denjhang/2xOPN-MegaMod-2023/2xOPN MegaMod v0.4/sshot-20231101-213623.png

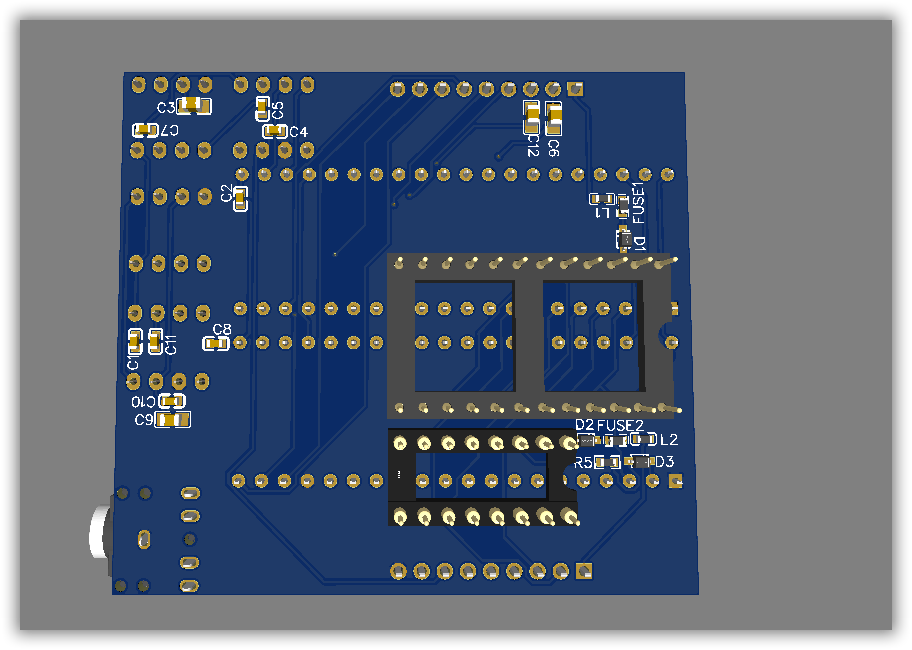
2xOPN MegaMod v0.4/sshot-20231101-213623.png
