denjhang/2xOPN-MegaMod-2023/2xOPN Mixer v0.2/sshot-20231115-143608.png

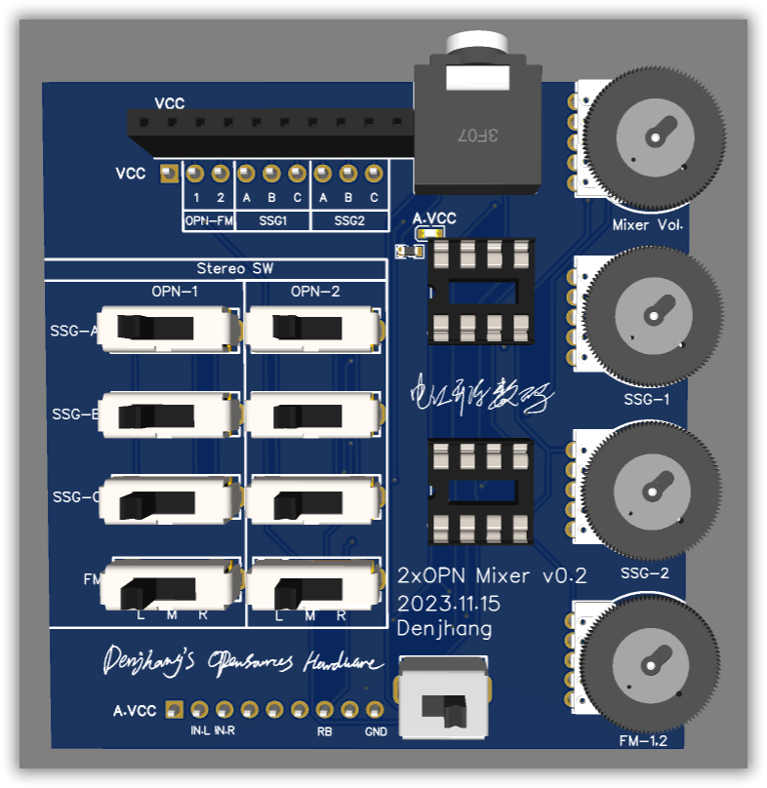
2xOPN Mixer v0.2/sshot-20231115-143608.png
