denjhang/2xOPN-MegaMod-2023/acb-gold-slice.png

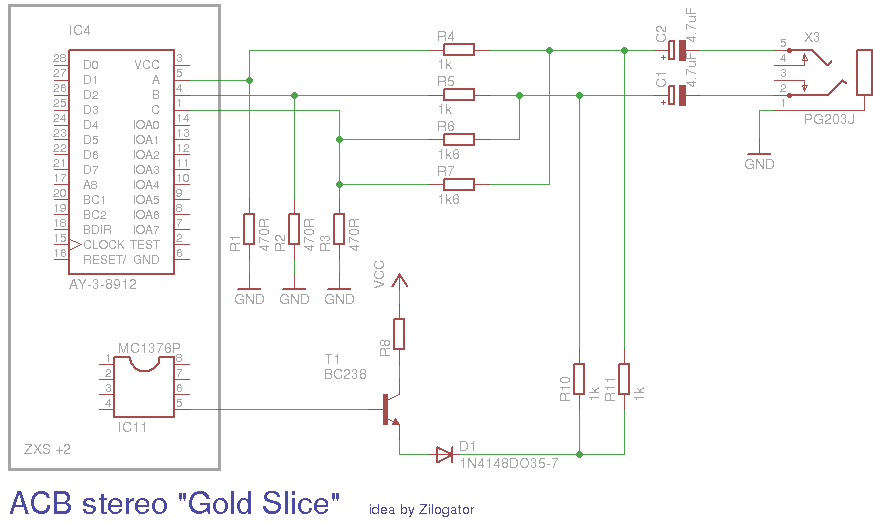
acb-gold-slice.png
