denjhang/2xOPN-MegaMod-2023/OPL2LPT-Replica-master/images/4.jpg

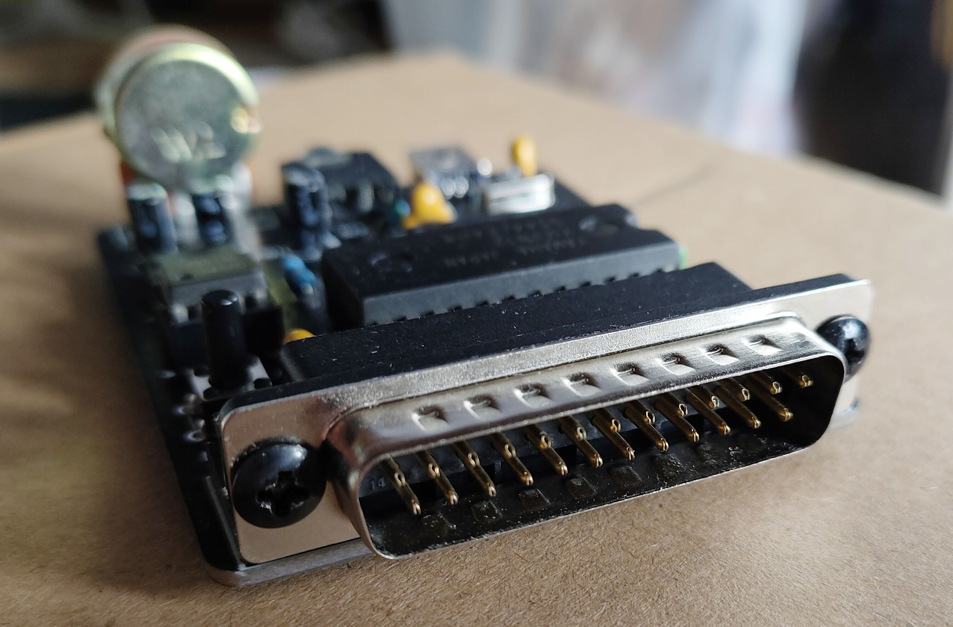
OPL2LPT-Replica-master/images/4.jpg
