denjhang/2xOPN-MegaMod-2023/rc2014-ym2149-main/R6-board-pic.jpg

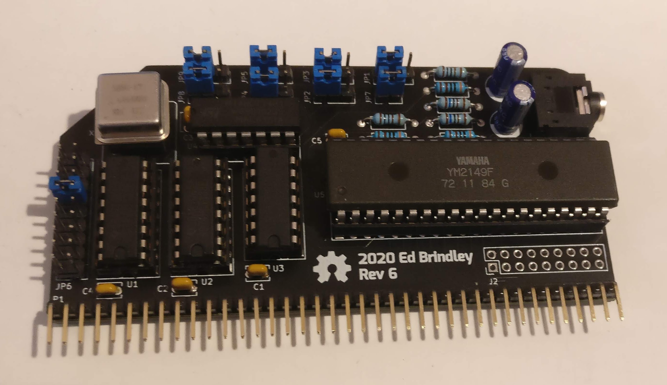
rc2014-ym2149-main/R6-board-pic.jpg
