denjhang/2xOPN-MegaMod-2023/rc2014-ym2149-main/r61-board-render.png

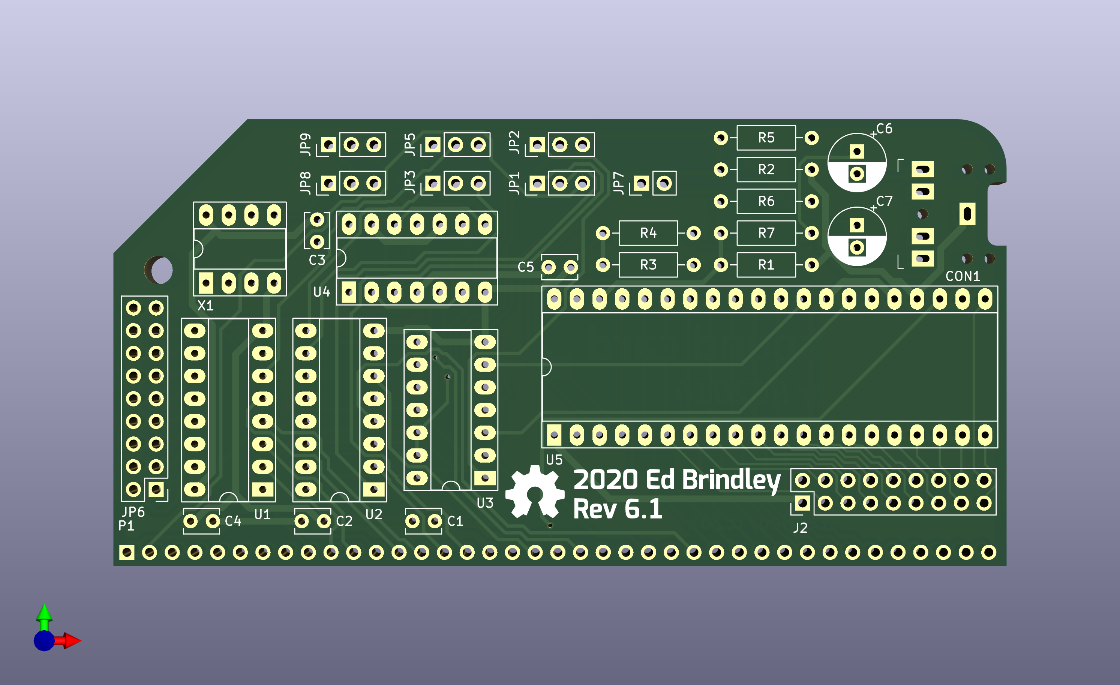
rc2014-ym2149-main/r61-board-render.png
