denjhang/2xOPN-MegaMod-2023/参考资料/ym2610-pcb-master/ym2610-pcb-master/photo/pcb2.jpg

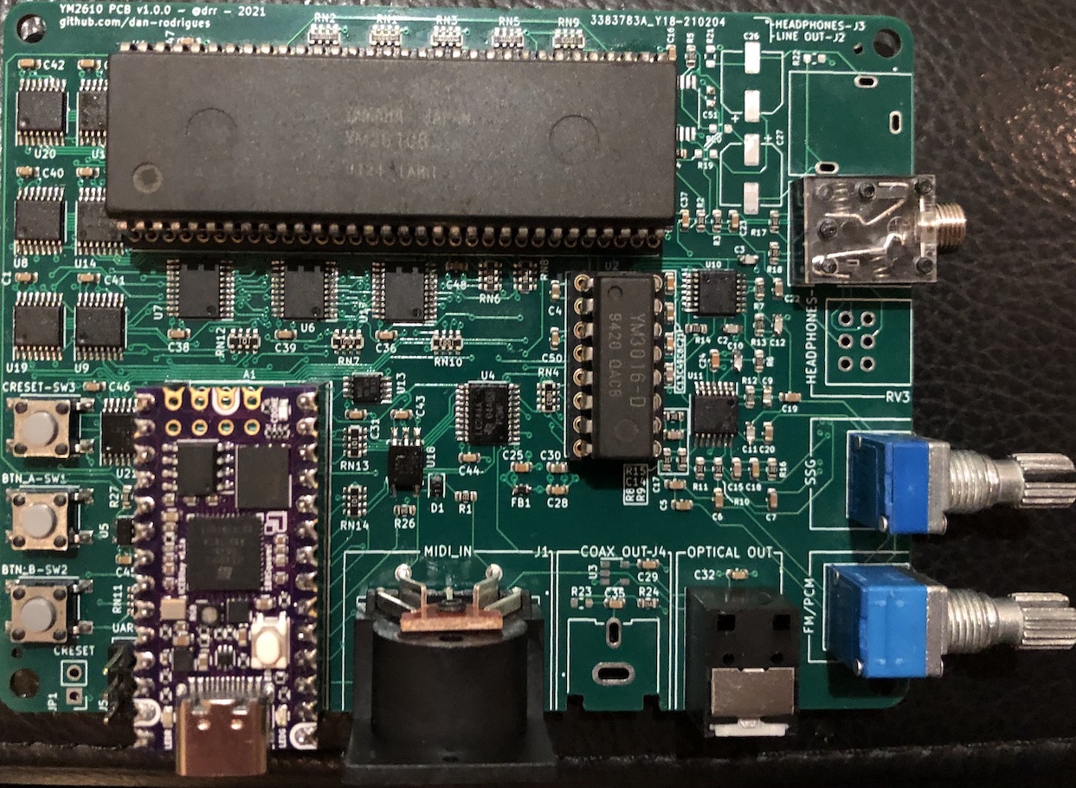
参考资料/ym2610-pcb-master/ym2610-pcb-master/photo/pcb2.jpg
