denjhang/2xOPN-MegaMod-2023/参考资料/ym2610-pcb-master/ym2610-pcb-master/pcb/ym2610-pcb.pdf

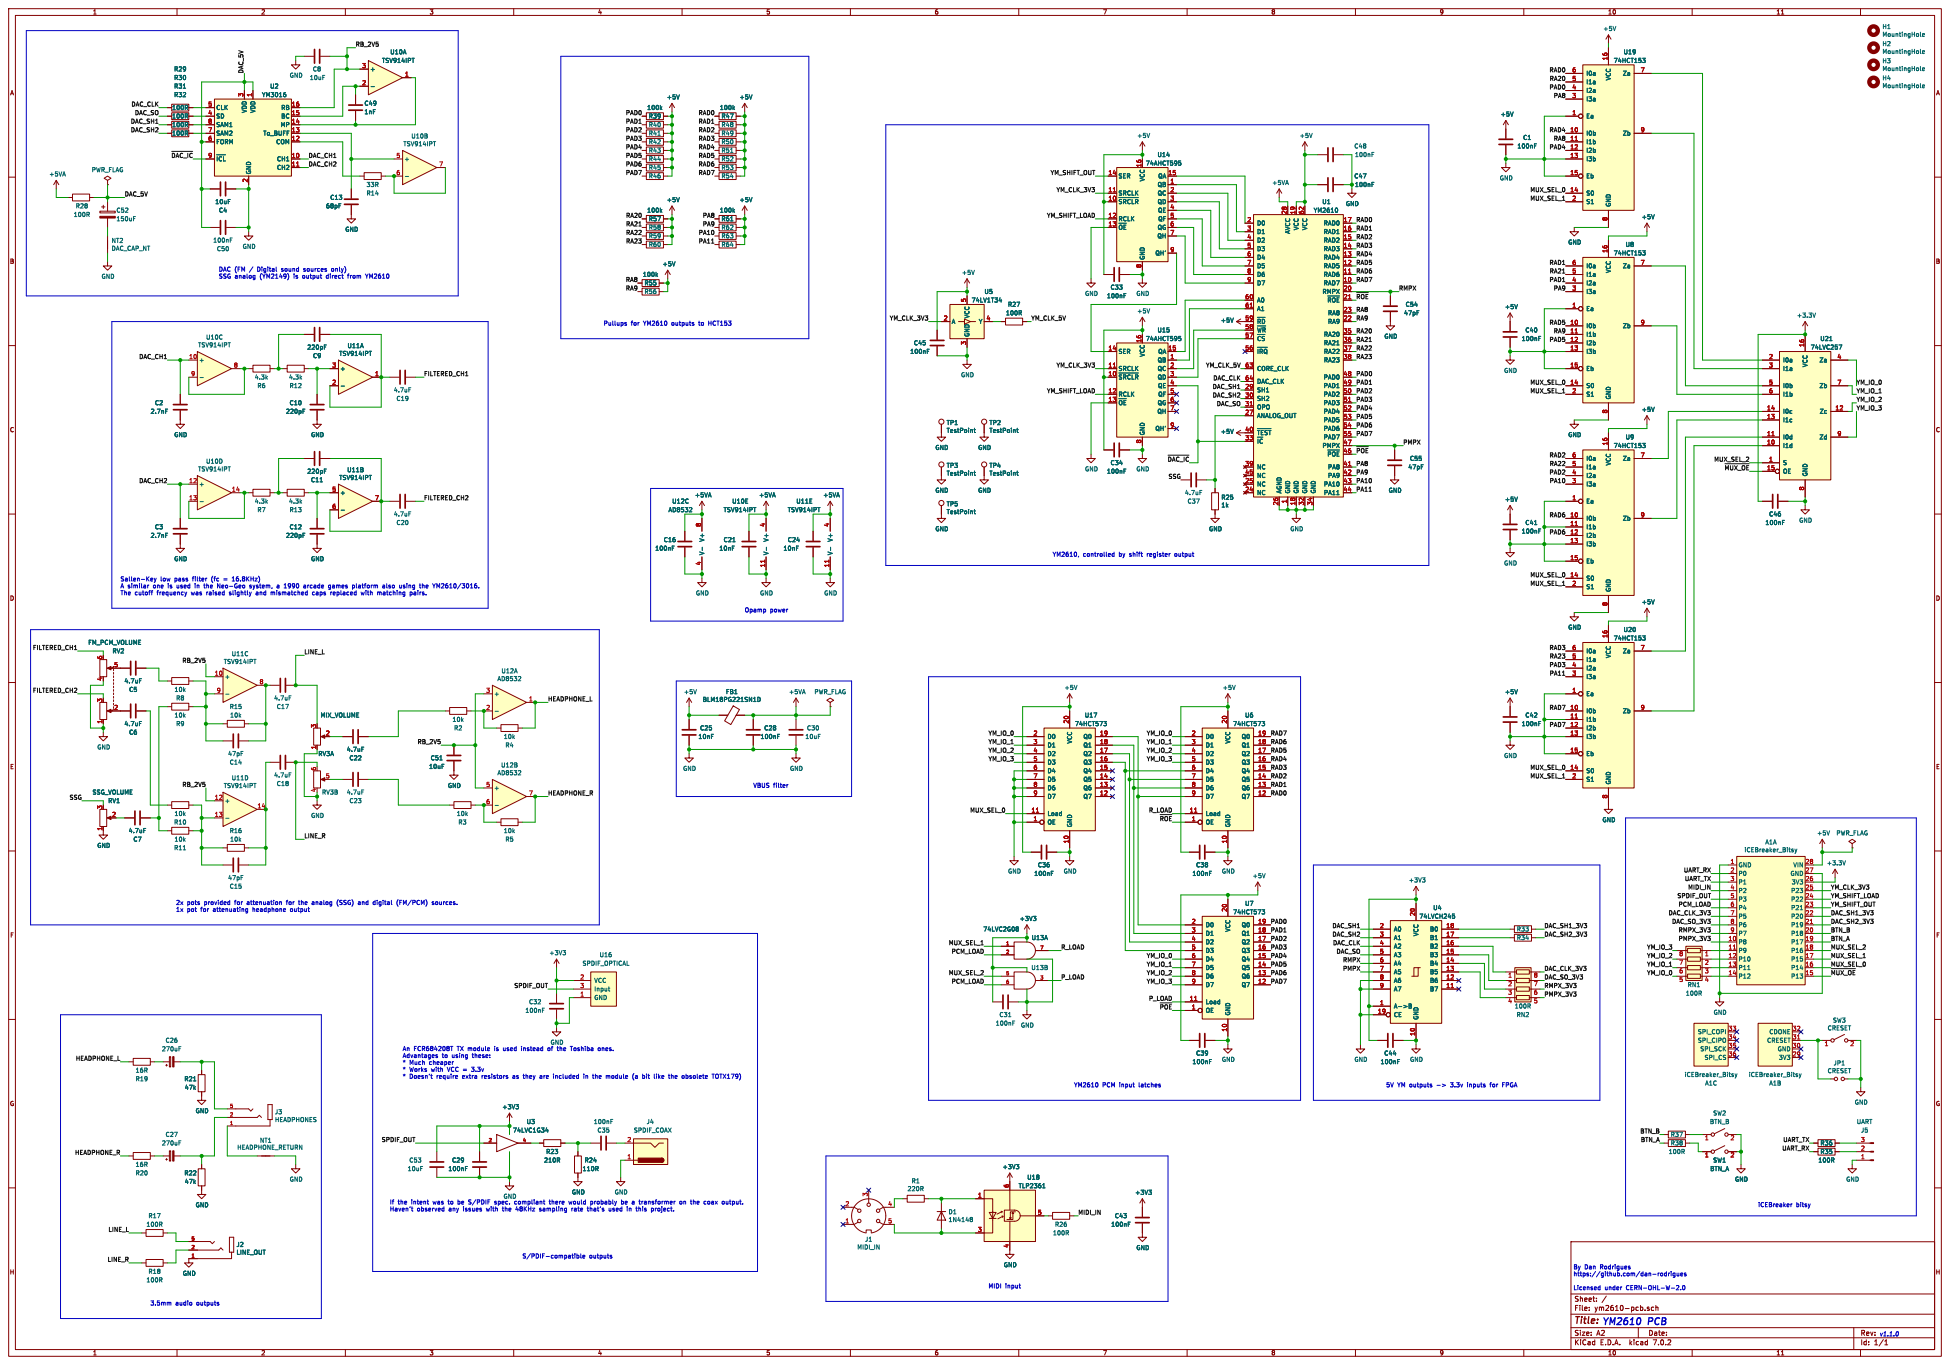
[picture p31: page 1]

H2 MountingHole H3 MountingHole H1 MountingHole H4 MountingHole

3 SD 4 CLK 5 FORM 6 SAM2 7 SAM1 8 ~{ICL} 9 U2 YM3016 GND GND

3 SD 4 CLK 5 FORM 6 SAM2 7 SAM1 8 ~{ICL} 9 GND

1 CH1 10 CH2 11 COM 12 To_BUFF 13 MP 14 BC 15 RB 16 GND
+5VA VDD

DAC (FM / Digital sound sources only) SSG analog (YM2149) is output direct from YM2610

Pullups for YM2610 outputs to HCT153

An FCR684208T TX module is used instead of the Toshiba ones. Advantages to using these: * Much cheaper * Works with VCC = 3.3v

https://github.com/dan-rodrigues Licensed under CERN-OHL-W-2.0

Id: 1/1 Title: File: ym2610-pcb.sch Sheet: /
YM2610 PCB
