denjhang/2xOPN-MegaMod-2023/2xOPN MegaMod v0.1/Schematic_Dual OPN MegaMod_2022-12-18.pdf

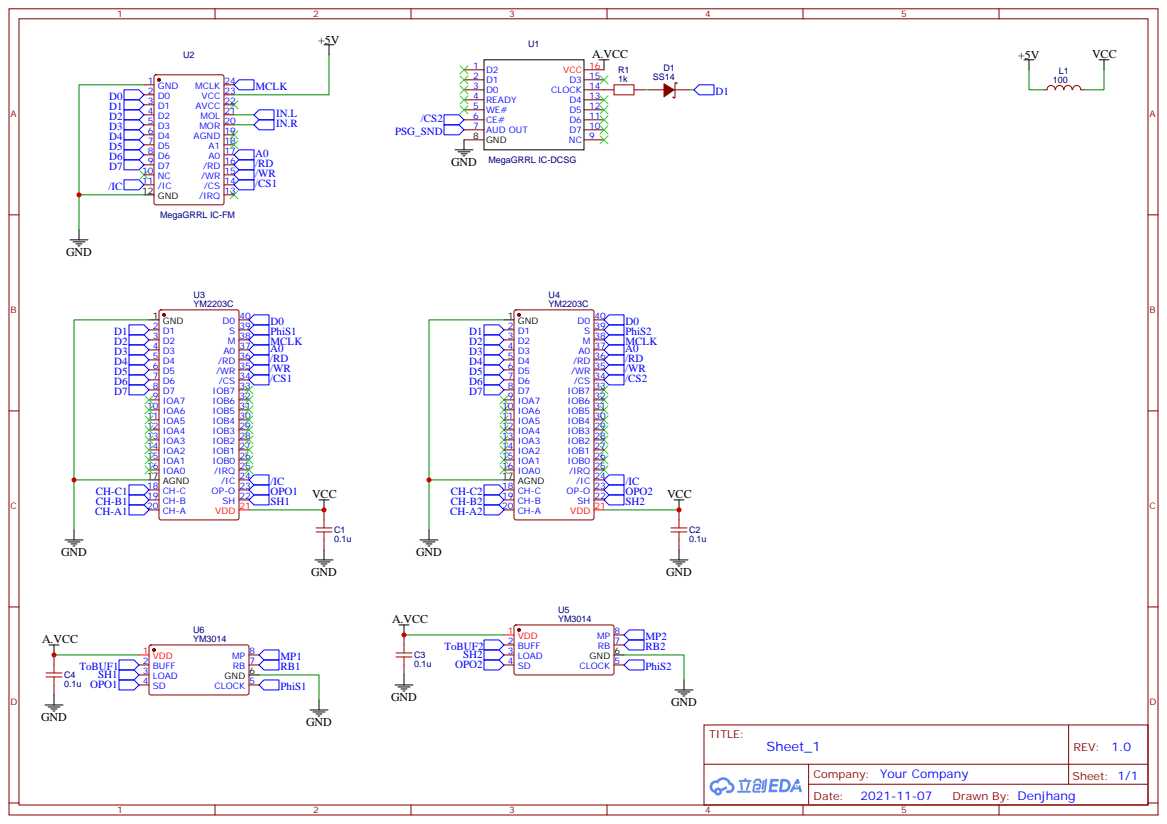
[picture p43: page 1]

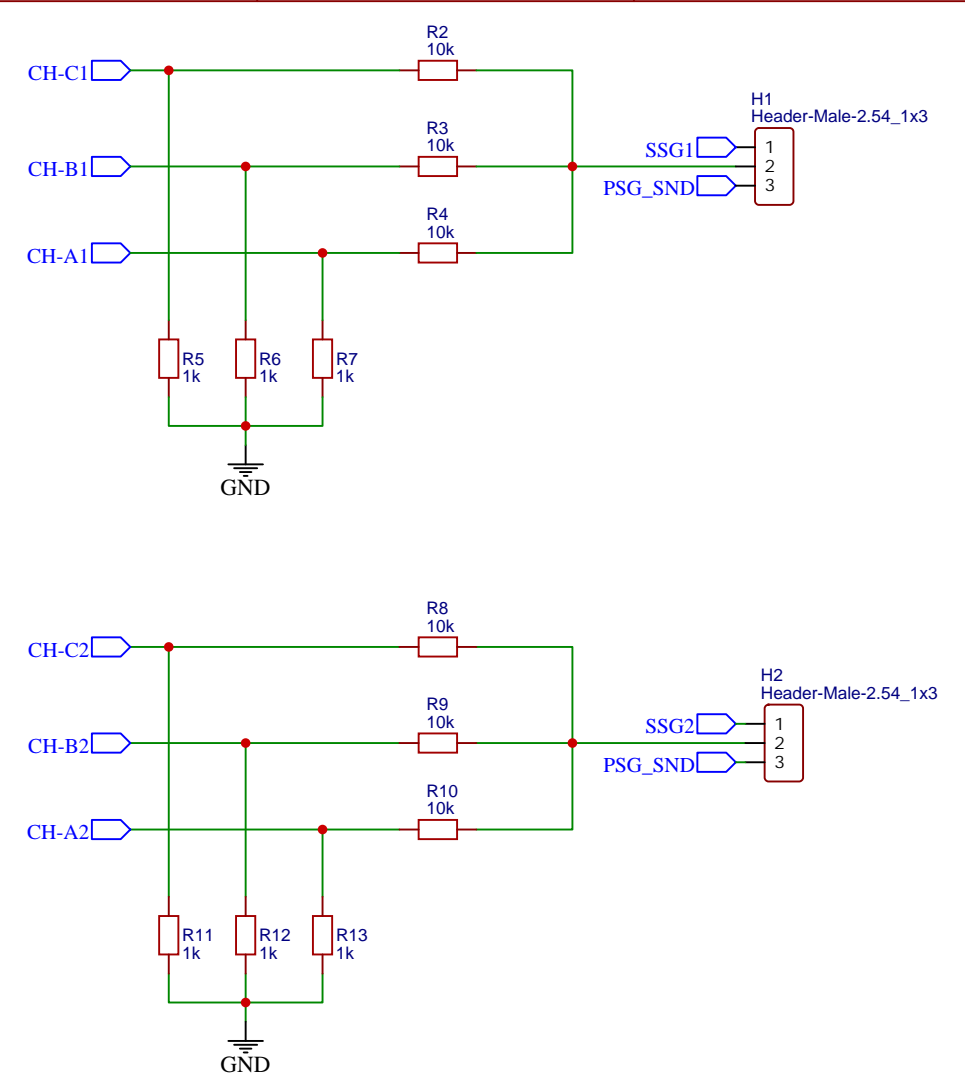
[picture p44: page 2]

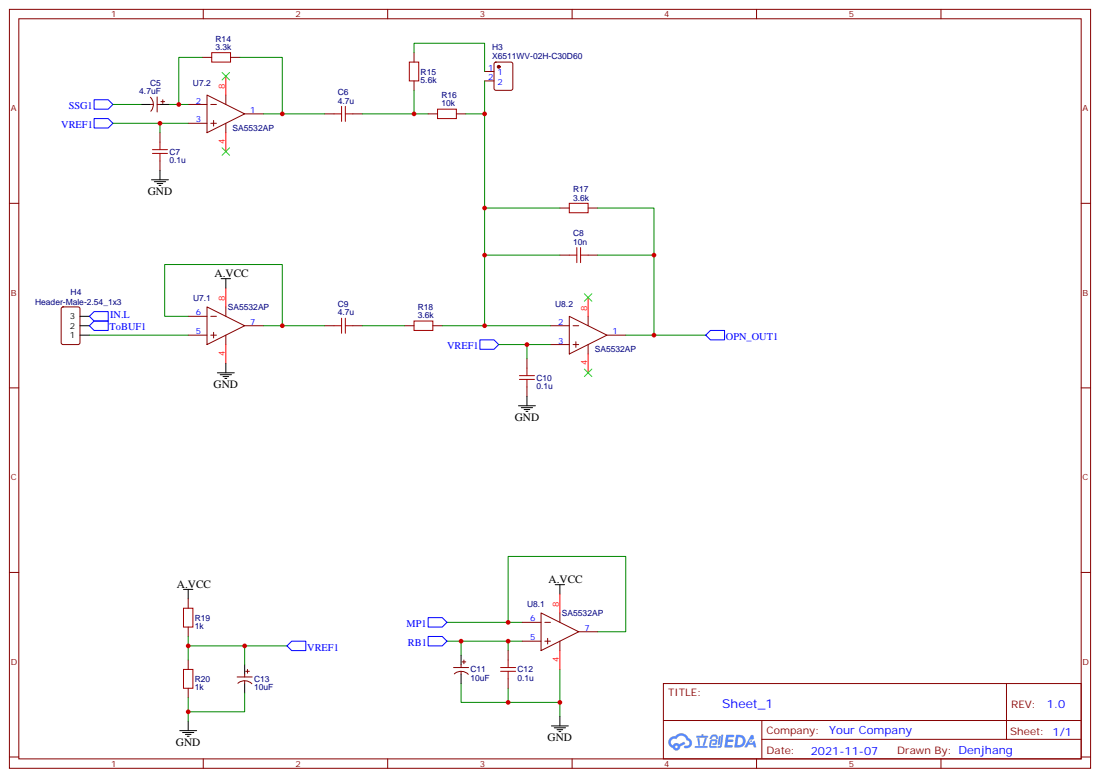
[picture p45: page 3]

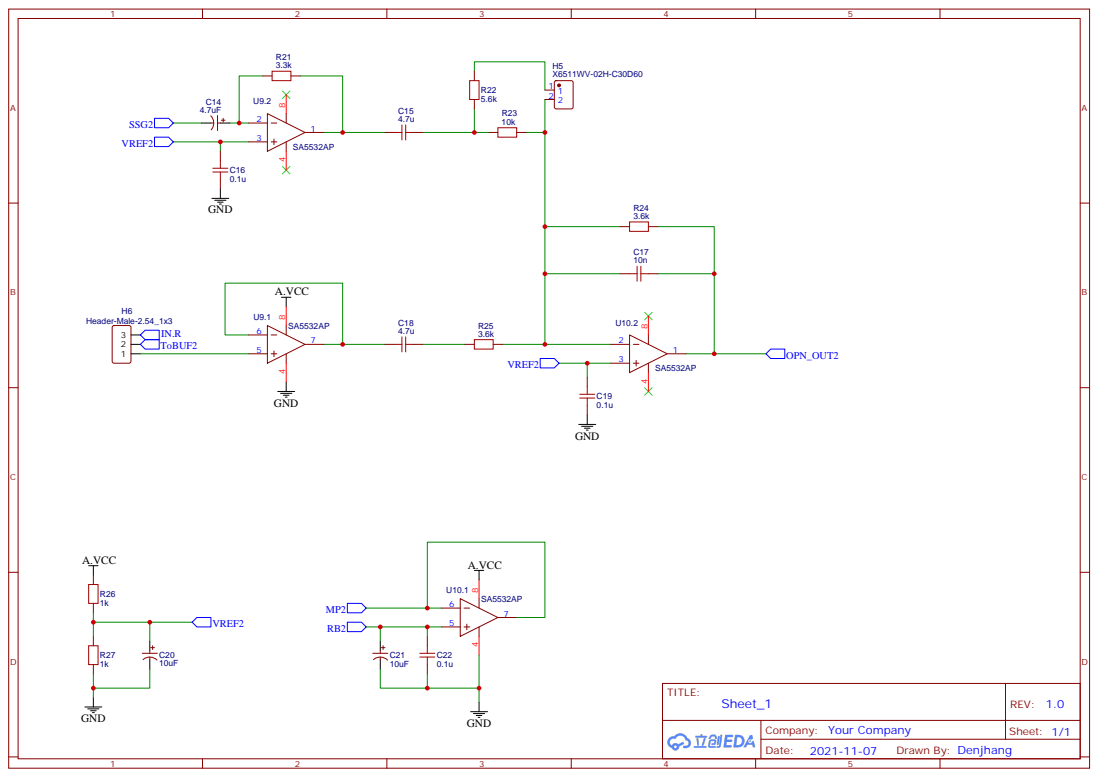
[picture p46: page 4]

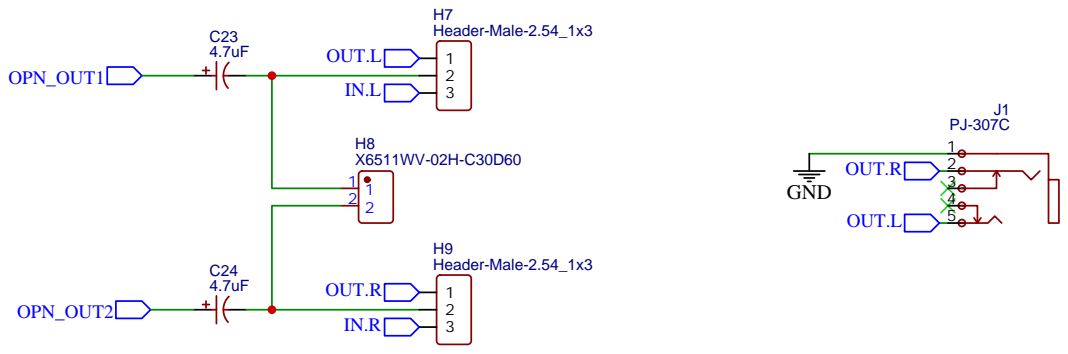
[picture p47: page 5]
