denjhang/2xOPN-MegaMod-2023/2xOPN MegaMod v0.2/Schematic_Dual OPN MegaMod v0.2_2023-01-27.pdf

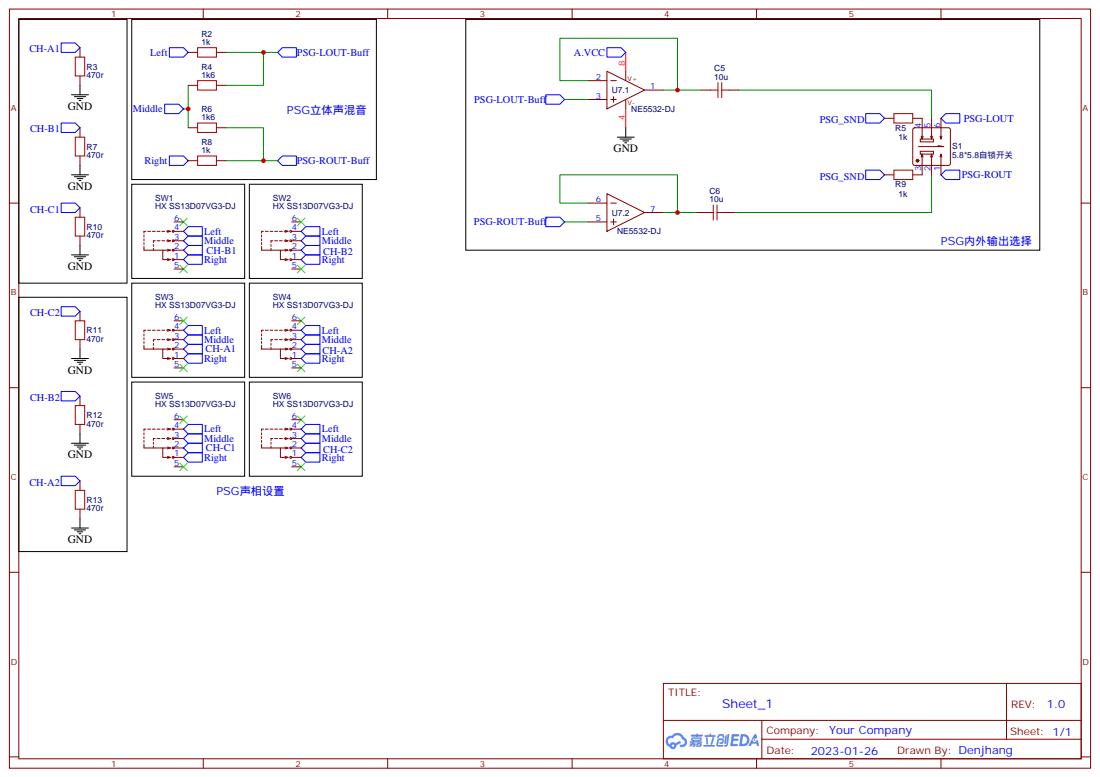
[picture p48: page 2]

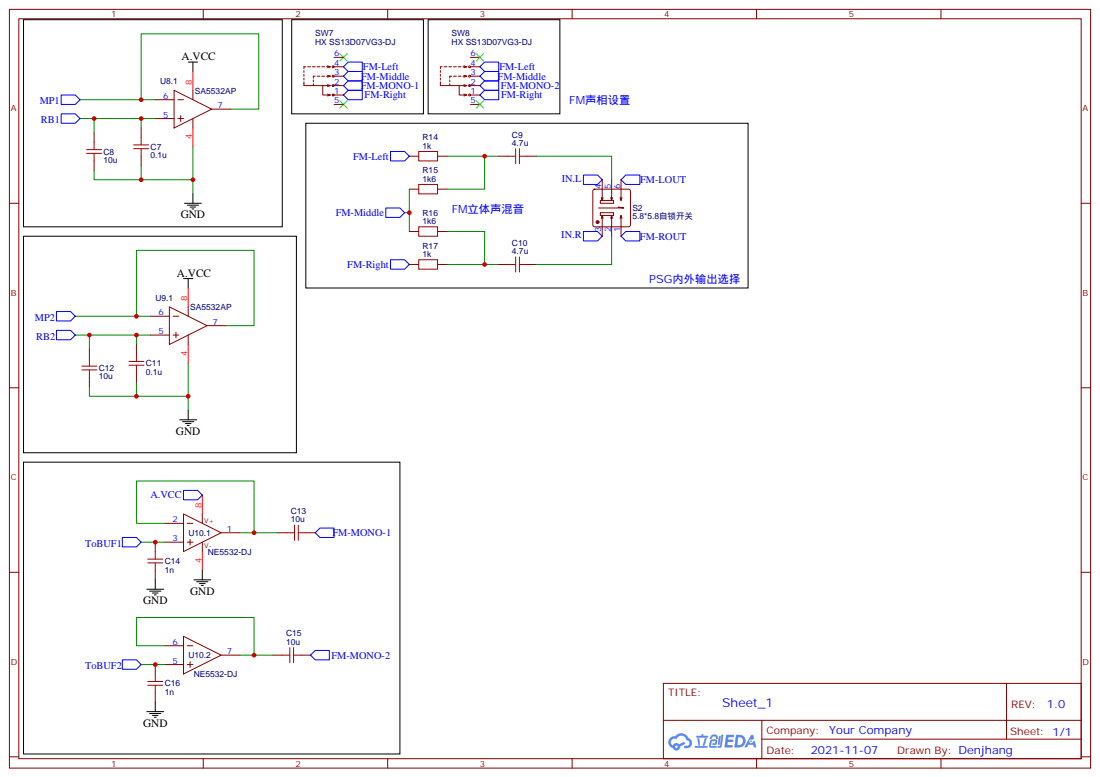
[picture p49: page 3]

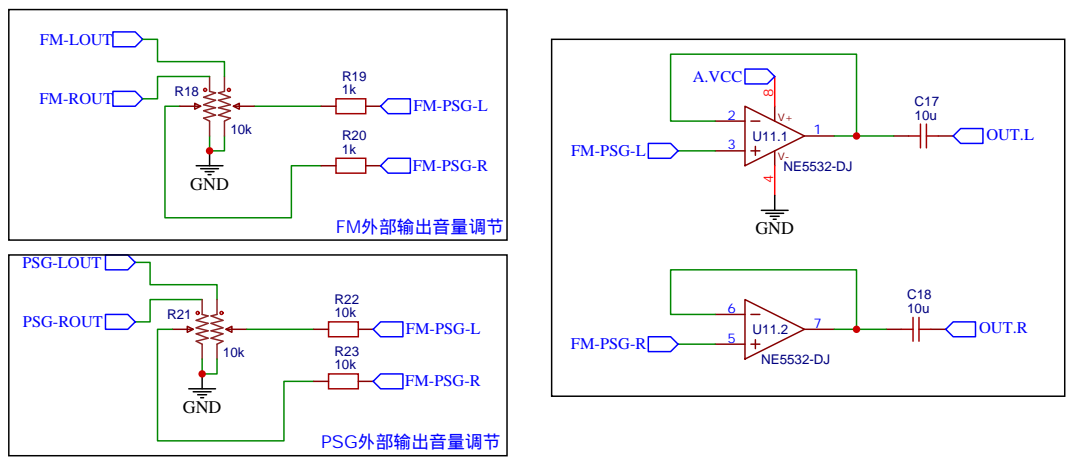
[picture p50: page 4]

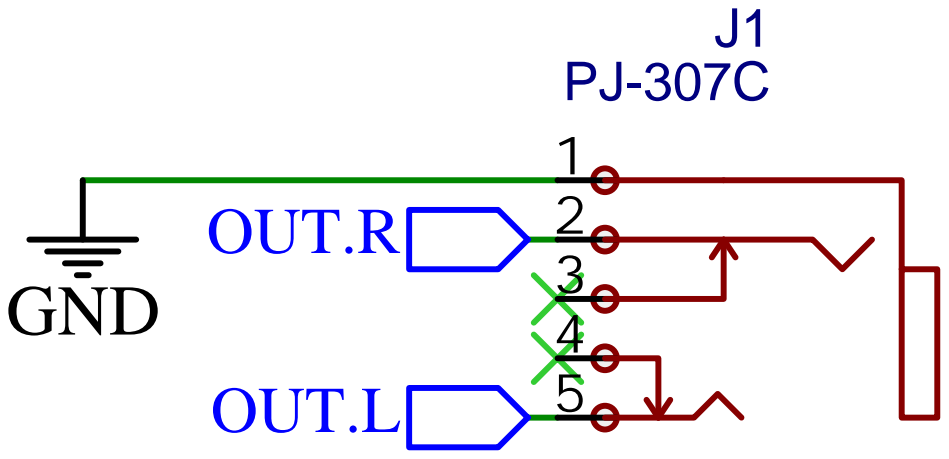
[picture p51: page 5]
